DumberThanUsual/FYP-IR-SENSOR/KiCad/IR Sensor Schematic.kicad_sch

## KiCad design KiCad/IR Sensor Schematic.kicad_sch (2024-05-24)

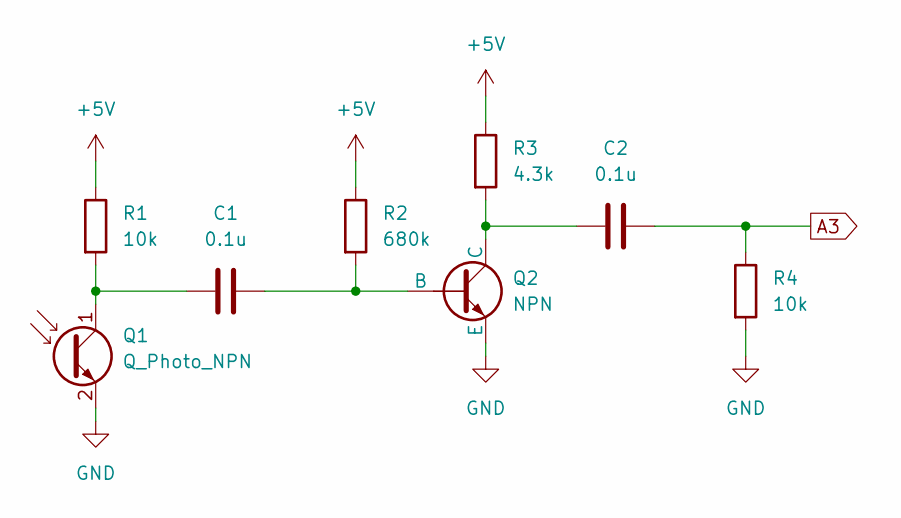
[picture p3: schematic IR Sensor Schematic.kicad_sch]

Parts:
C1, C2: 0.1u
Q1: Q_Photo_NPN
Q2: NPN
R1, R4: 10k
R2: 680k
R3: 4.3k

Connections:
+5V: R1.1, R2.1, R3.1
A3: C2.2, R4.1
GND: Q1.2 (E), Q2.3 (E), R4.2
unnamed: C1.1, Q1.1 (C), R1.2
unnamed: C1.2, Q2.2 (B), R2.2
unnamed: C2.1, Q2.1 (C), R3.2
